manweile/ESP32_Scale/PropaneScale/src/eeprom_store.cpp

/**
 * @file eeprom_store.cpp
 * @author Gerald Manweiler
 *
 * @brief EEPROM storage functions for the propane scale project.
 *
 * @details Implements eeprom functions to load, save & validate calibration factors, known weights, maximum propane weight, and tank tare.
 *
 * @version 0.1
 * @date 2026-05-06
 *
 * @copyright Copyright (c) 2026 Gerald Manweiler
 */

// Standard library headers
#include <Arduino.h>
#include <EEPROM.h>

// Local library headers
#include "config.h"
#include "eeprom_store.h"
#include "parsing_utils.h"
#include "scale_io.h"

// External Global State Variables
extern bool eepromReady;                                   // Flag to track if EEPROM was successfully initialized

// Definitions of EEPROM storage functions for the propane scale project

bool loadFromEeprom(float& value, uint32_t magicAddr, uint32_t magicValue, uint32_t valueAddr)
{
  uint32_t magic = 0;                                       // Magic number read from EEPROM for validation

  EEPROM.get(magicAddr, magic);

  if (magic != magicValue) {
    return false;
  }

  EEPROM.get(valueAddr, value);
  return true;
}

bool printEepromField(const char* label, uint32_t magicAddr, uint32_t magicValue, uint32_t valueAddr, float minValue, float maxValue, bool useAbsMag,
                      const char* unitSuffix)
{
  float value = 0.0f;
  char line[96];

  if (loadFromEeprom(value, magicAddr, magicValue, valueAddr) && isValidBoundedFloat(value, minValue, maxValue, useAbsMag)) {
    snprintf(line, sizeof(line), "%s: %.2f%s\n",
             label,
             value,
             (unitSuffix != nullptr && unitSuffix[0] != '\0') ? unitSuffix : "");
    queueSerialOutput(line);
    return true;
  }

  snprintf(line, sizeof(line), "%s: <invalid or not set>\n", label);
  queueSerialOutput(line);
  return false;
}

bool saveToEeprom(float value, uint32_t magic, int magicAddr, int valueAddr)
{
  if (!eepromReady) {
    return false;
  }

  EEPROM.put(magicAddr, magic);
  EEPROM.put(valueAddr, value);
  return EEPROM.commit();
}
